sparkfun/SparkFun_GNSS_LG580P/docs/assets/3d_model/poster.png

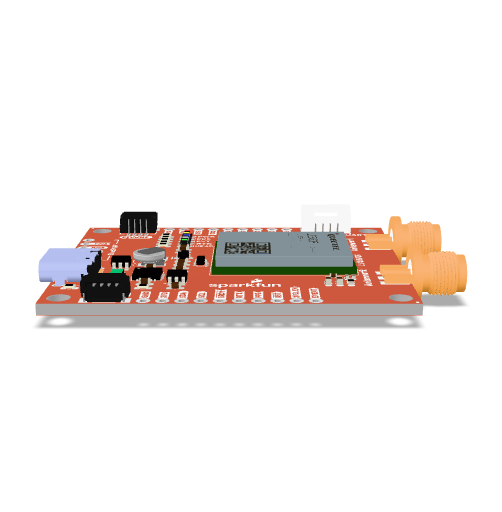
docs/assets/3d_model/poster.png
