sparkfun/SparkFun_GNSS_LG580P/docs/assets/board_files/dimensions2.png

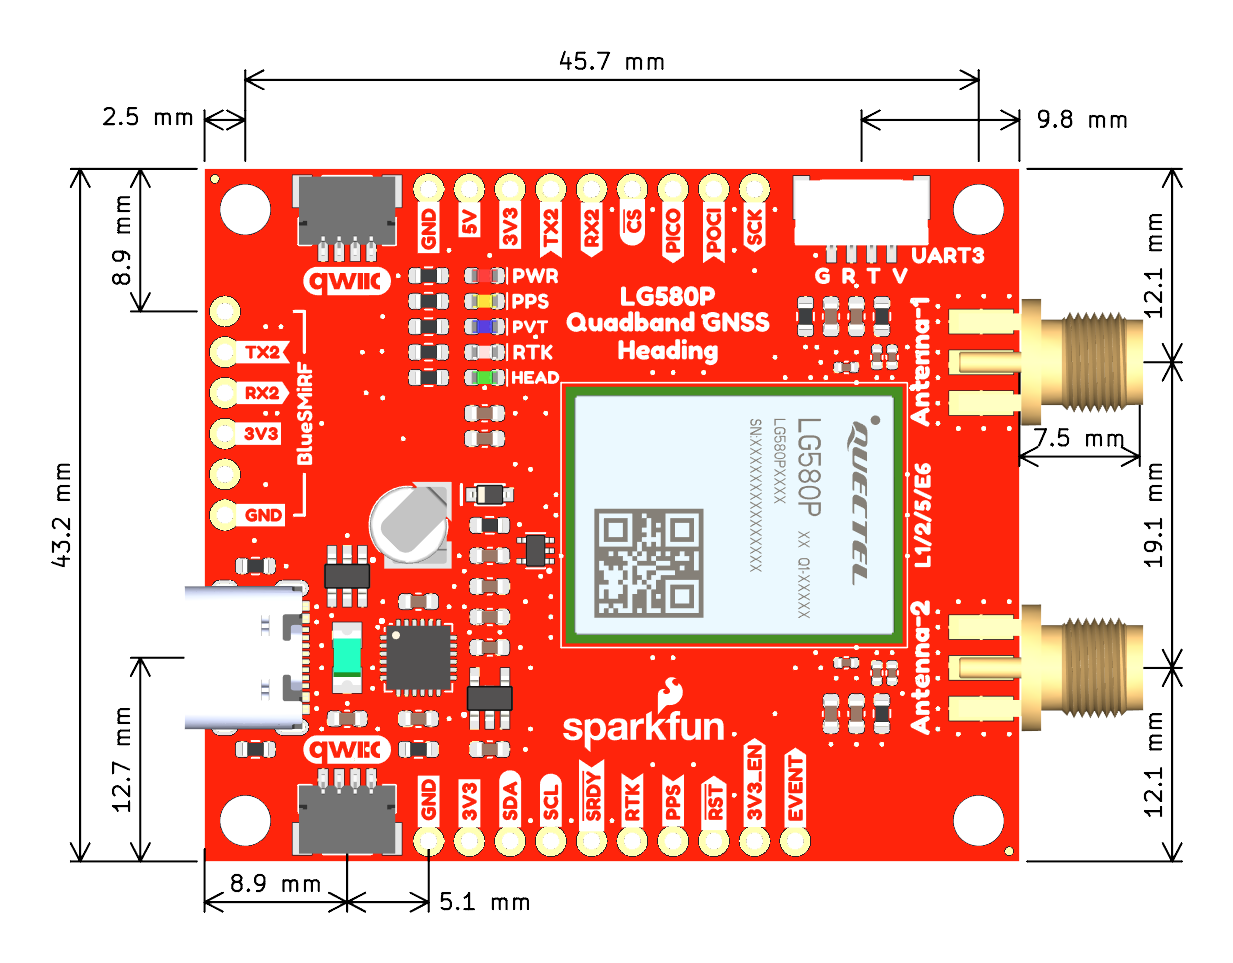
docs/assets/board_files/dimensions2.png
