sparkfun/SparkFun_GNSS_LG580P/docs/assets/img/hookup_guide/assembly-gnss_antenna-split.jpg

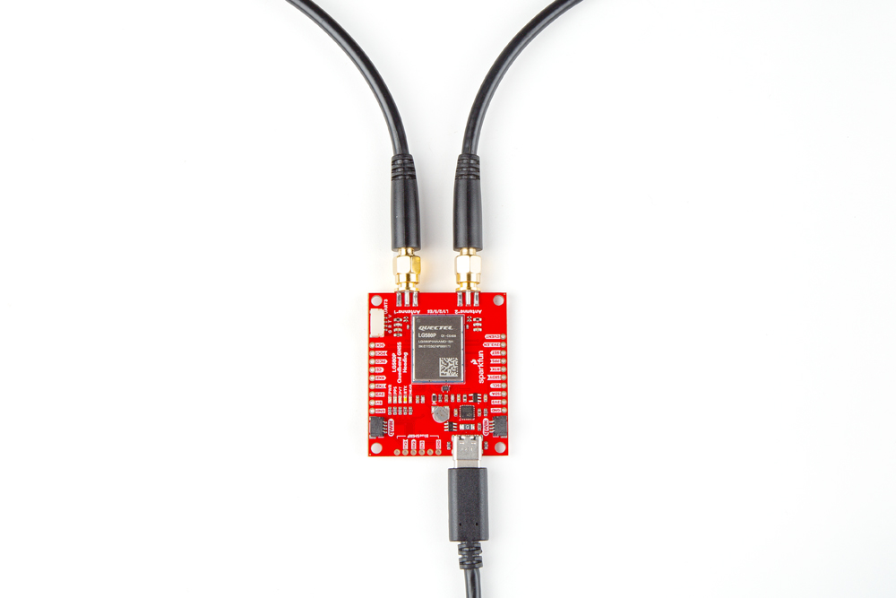
docs/assets/img/hookup_guide/assembly-gnss_antenna-split.jpg
